tallman5/rain-gauge/images/ESP8266-bottom.jpg

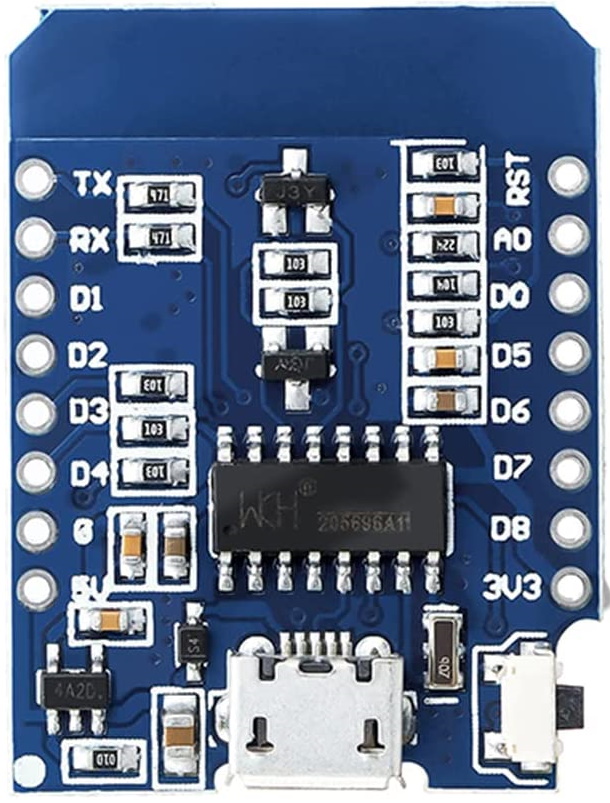
images/ESP8266-bottom.jpg
