tallman5/rain-gauge/images/ESP8266.jpg

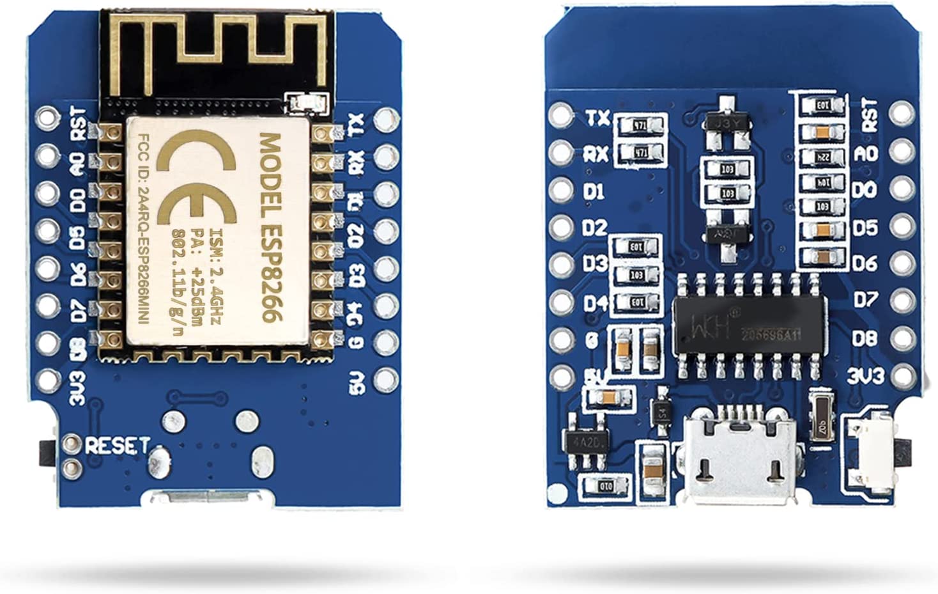
images/ESP8266.jpg
