tallman5/rain-gauge/images/rain-gauge-render.png

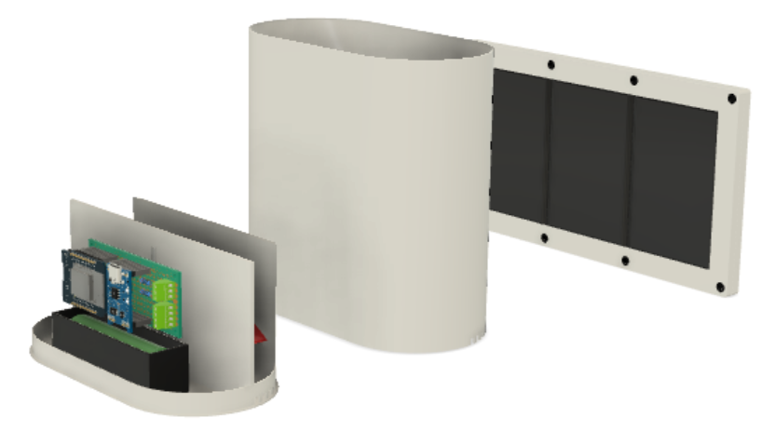
images/rain-gauge-render.png
