tallman5/rain-gauge/images/rain-gauge-thumb.png

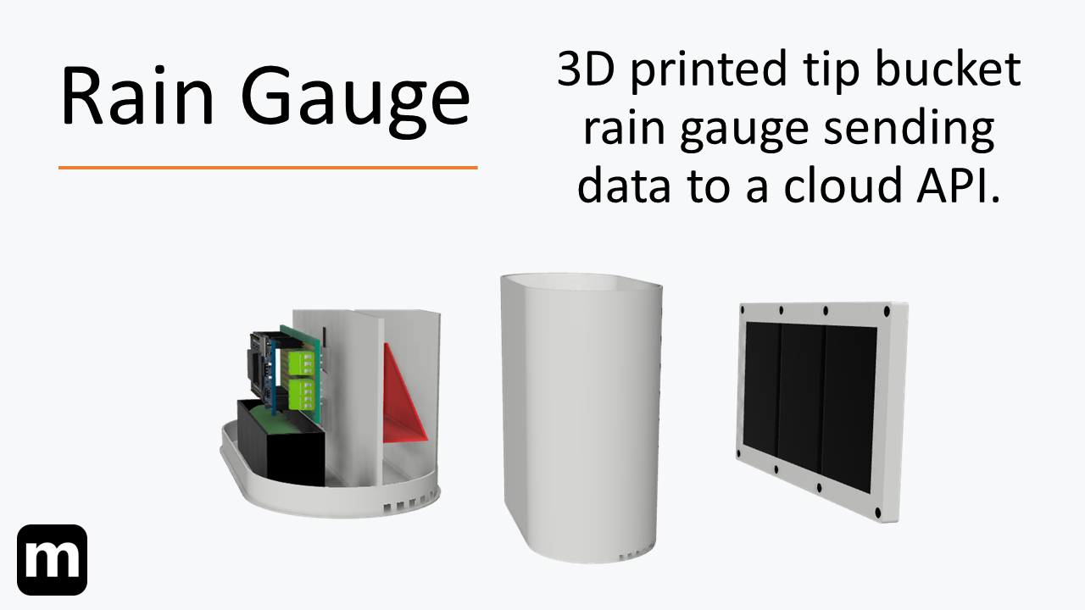
images/rain-gauge-thumb.png
