tallman5/rain-gauge/images/solar-panel.jpg

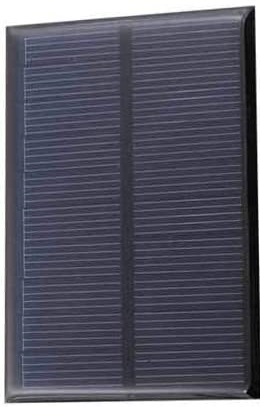
images/solar-panel.jpg
