tallman5/rain-gauge/images/TP4056.jpg

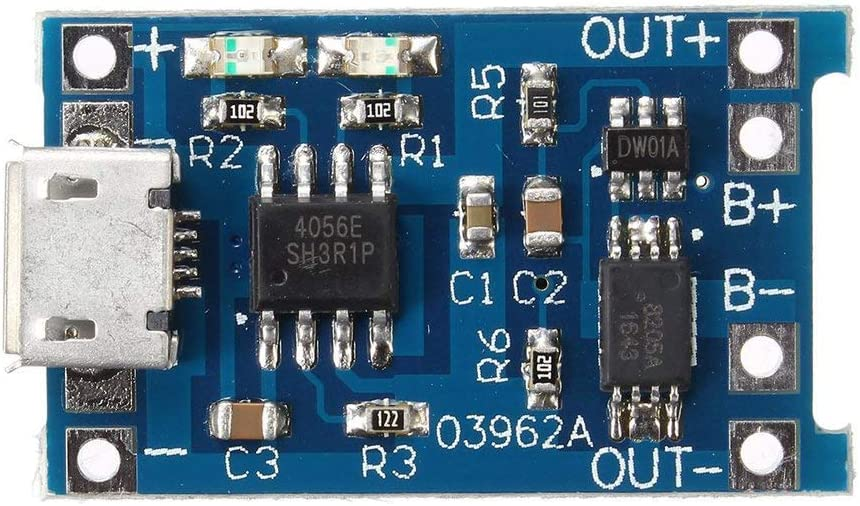
images/TP4056.jpg
